dmaone/CommonSense/cortex/PSoC5/io.c

/*
 *
 * Copyright (C) 2016-2017 DMA <dma@ya.ru>
 *
 * This program is free software; you can redistribute it and/or modify
 * it under the terms of the GNU General Public License version 2 as
 * published by the Free Software Foundation.
 */
#include "../io.h"

#include <project.h>
#include <stdio.h>

#include "../gpio.h"
#include "../globals.h"
#include "../scan.h"
#include "../settings.h"

// for xprintf - stdio + stdarg
#include <stdarg.h>

// only allow telemetry every Nth USB tick - see io_has_space.
// This is needed so host isn't too overwhelmed to timely send GET_STATUS
// (if it doesn't - keyboard goes to autonomous mode and telemetry stops!)
#define TELEMETRY_RATELIMIT 10
volatile uint8_t telemetry_cooldown = TELEMETRY_RATELIMIT;  // Block until first io_tick

static bool boot_protocol_mode = false;

typedef struct {
  uint8_t EP;
  uint8_t len;
  uint8_t data[64];
} UsbPdu_t;

#define USB_BUFFER_END 15
#define USB_BUFFER_NEXT(X) ((X + 1) & USB_BUFFER_END)
#define USB_BUFFER_PREV(X) ((X + USB_BUFFER_END) & USB_BUFFER_END)
// ^^^ THIS MUST EQUAL 2^n-1!!! Used as bitmask.

#define KBD_INTERFACE 0
#define KBD_SCB USB_DEVICE0_CONFIGURATION0_INTERFACE0_ALTERNATE0_HID_OUT_RPT_SCB
#define KBD_INBOX USB_DEVICE0_CONFIGURATION0_INTERFACE0_ALTERNATE0_HID_OUT_BUF
#define KBD_OUTBOX USB_DEVICE0_CONFIGURATION0_INTERFACE0_ALTERNATE0_HID_IN_BUF

#define CONSUMER_OUTBOX                                                        \
  USB_DEVICE0_CONFIGURATION0_INTERFACE2_ALTERNATE0_HID_IN_BUF

#define SYSTEM_OUTBOX                                                          \
  USB_DEVICE0_CONFIGURATION0_INTERFACE3_ALTERNATE0_HID_IN_BUF

#define CTRLR_SCB                                                              \
  USB_DEVICE0_CONFIGURATION0_INTERFACE1_ALTERNATE0_HID_OUT_RPT_SCB
#define CTRLR_INBOX USB_DEVICE0_CONFIGURATION0_INTERFACE1_ALTERNATE0_HID_OUT_BUF

UsbPdu_t usbSendingQueue[USB_BUFFER_END + 1];
uint8_t usbSendingReadPos = 0;
uint8_t usbSendingWritePos = 0;

void report_status(void) {
  IN_c2packet_t outbox;
  outbox.response_type = C2RESPONSE_STATUS;
  device_status_t* deviceStatus = (void *)&outbox.payload;
  deviceStatus->status = status_register;
  deviceStatus->versionMajor = DEVICE_VER_MAJOR;
  deviceStatus->versionMinor = DEVICE_VER_MINOR;
  EEPROM_UpdateTemperature();
  deviceStatus->dieTempSign = dieTemperature[0];
  deviceStatus->dieTemp = dieTemperature[1];
  deviceStatus->sysTime = systime;
  io_c2(&outbox);
  // xprintf("time: %d", systime);
  // xprintf("LED status: %d %d %d %d %d", led_status&0x01, led_status&0x02,
  // led_status&0x04, led_status&0x08, led_status&0x10);
}

void process_ewo(OUT_c2packet_t *inbox) {
  bool scan_active = STATUS_IS(C2DEVSTATUS_SCAN_ENABLED);
  status_register = inbox->payload[0];
  // Avoid scan_start if already started - dangerous to do so.
  if (!scan_active && STATUS_IS(C2DEVSTATUS_SCAN_ENABLED)) {
    scan_start();
  }
  report_status();
}

void usb_receive(OUT_c2packet_t *inbox) {
  ticksToAutonomy = SETUP_TIMEOUT;
  switch (inbox->command) {
  case C2CMD_EWO:
    process_ewo(inbox);
    break;
  case C2CMD_GET_STATUS:
    report_status();
    if (STATUS_IS(C2DEVSTATUS_INSANE)) {
      scan_report_insanity();
    }
    break;
  case C2CMD_SET_MODE:
    FORCE_BIT(status_register, C2DEVSTATUS_SETUP_MODE, inbox->payload[0]);
    report_status(); // If FC doesn't get a reply - it will wait 2s for CTS.
    break;
  case C2CMD_ENTER_BOOTLOADER:
    xprintf("Jumping to bootloader..");
    Boot_Load(); // Does not return, no need for break
  case C2CMD_UPLOAD_CONFIG:
    settings_receive_block(inbox);
    break;
  case C2CMD_DOWNLOAD_CONFIG:
    settings_send_block(inbox);
    break;
  case C2CMD_APPLY_CONFIG:
    xprintf("Applying config..");
    SET_BIT(status_register, C2DEVSTATUS_SETUP_MODE);
    settings_apply();
    xprintf("success!");
    break;
  case C2CMD_COMMIT:
    settings_save();
    break;
  case C2CMD_ROLLBACK:
    xprintf("Resetting..");
    CySoftwareReset(); // Does not return, no need for break.
  case C2CMD_ENABLE_TELEMETRY:
    FORCE_BIT(status_register, C2DEVSTATUS_TELEMETRY_MODE, inbox->payload[0]);
    FORCE_BIT(status_register, C2DEVSTATUS_SETUP_MODE, !inbox->payload[0]);
    scan_reset();
    if (!inbox->payload[0]) {
      report_status(); // FC wants reply - if telemetry is off, send status.
    }
    break;
  default:
    break;
  }
}

void usbEnqueue(uint8_t EP, uint8_t len, uint8_t *data) {
  usbSendingWritePos = USB_BUFFER_NEXT(usbSendingWritePos);
  usbSendingQueue[usbSendingWritePos].EP = EP;
  usbSendingQueue[usbSendingWritePos].len = len;
  memcpy(usbSendingQueue[usbSendingWritePos].data, data, len);
}

void usbSend() {
  if (usb_status != USB_STATUS_CONNECTED) {
    return;
  }
  while (usbSendingWritePos != usbSendingReadPos) {
    uint8_t pos = USB_BUFFER_NEXT(usbSendingReadPos);
    UsbPdu_t* item = &usbSendingQueue[pos];
    if (USB_GetEPState(item->EP) == USB_IN_BUFFER_EMPTY) {
      if (boot_protocol_mode && item->EP == KBD_EP) {
        /*
         * In boot protocol mode, send short packets, lest HP Z800 BIOS
         * will get first key stuck until you unplug the keyboard.
         *
         * Which is kinda violation of USB HID Appendix B
         * ("The BIOS will ignore any extensions to reports")
         * but also kinda not ("The report may not exceed 8 bytes in length.")
         * Most BIOSes are fine with 64-byte USB packets, but not HP Z800.
         */
        USB_LoadInEP(item->EP, item->data, 8);
      } else {
        USB_LoadInEP(item->EP, item->data, item->len);
      }
      usbSendingReadPos = pos;
    } else {
      break;
    }
  }
}

bool io_has_space(void) {
  // figuring out if IO is busy based on queue length doesn't work.
  // So we'll just ratelimit to every 10th tick
  if (telemetry_cooldown == 0) {
    telemetry_cooldown = 1;
    return true;
  }
  return false;
}

void io_init(void) {
  usbSendingReadPos = 0;
  usbSendingWritePos = 0;
  pipeline_init();
#ifndef SELF_POWERED
  USB_Start(0u, USB_5V_OPERATION);
#endif
}

void io_tick(void) {
  /* This doesn't work - supposed to, but doesn't.
  if (USB_GetEPState(OUTBOX_EP) == USB_OUT_BUFFER_FULL) {
    OUT_c2packet_t inbox;
    USB_ReadOutEP(OUTBOX_EP, inbox.raw, 64);
    usb_receive(&inbox);
  }
  if (USB_GetEPState(KBD_EP) == USB_OUT_BUFFER_FULL) {
    led_status = KBD_INBOX[0];
    KBD_SCB.status = USB_XFER_IDLE;
    gpio_setLEDs(led_status);
  }
  */
  uint8_t enableInterrupts = CyEnterCriticalSection();
  if (CTRLR_SCB.status == USB_XFER_STATUS_ACK) {
    CTRLR_SCB.status = USB_XFER_IDLE;
    usb_receive((OUT_c2packet_t*)CTRLR_INBOX);
  }
  if (KBD_SCB.status == USB_XFER_STATUS_ACK) {
    led_status = KBD_INBOX[0];
    KBD_SCB.status = USB_XFER_IDLE;
    gpio_setLEDs(led_status);
  }
  CyExitCriticalSection(enableInterrupts);
  if (USB_GetProtocol(KBD_INTERFACE) == 0) {
    io_kro_limit = BOOT_KRO_LIMIT;
    boot_protocol_mode = true;
  } else {
    boot_protocol_mode = false;
    io_kro_limit = KBD_KRO_LIMIT;
    /*
     * honoring SET_IDLE causes M1 MBP to spend 7% of CPU in com.apple.AppleUserHIDDrivers.
     * BLE HID docs say SET_IDLE was meant for autorepeat and is a Bad Idea in modern day.
     * So, this part is disabled.
    if (USB_UpdateHIDTimer(KBD_INTERFACE) == USB_IDLE_TIMER_EXPIRED) {
      // We must report periodically even if no change happened (USB HID 7.2.4)
      // ..except at least Windows just tells us to shut up forever,
      // only reporting when a real change happens.
      io_keyboard();
      io_consumer();
      io_system();
    }
    */
  }
  if (telemetry_cooldown > 0) {
    if (++telemetry_cooldown > TELEMETRY_RATELIMIT) {
      telemetry_cooldown = 0;
    }
  }
  usbSend();
}

void xprintf(const char *format_p, ...) {
#ifndef XPRINTF_ALWAYS_ENABLED
  if (BIT_IS_CLEAR(status_register, C2DEVSTATUS_SETUP_MODE)) {
    return;
  }
#endif
  IN_c2packet_t outbox;
  va_list va;
  va_start(va, format_p);
  vsnprintf((char *)outbox.raw, sizeof(outbox), format_p, va);
  va_end(va);
  io_c2(&outbox);
}

// Auto-timestamped xprintf
void ts_xprintf(const char *format_p, ...) {
#ifndef XPRINTF_ALWAYS_ENABLED
  if (BIT_IS_CLEAR(status_register, C2DEVSTATUS_SETUP_MODE)) {
    return;
  }
#endif
  IN_c2packet_t outbox;
  va_list va;
  va_start(va, format_p);
  log_message_t* msg = (log_message_t*)&outbox.raw;
  vsnprintf(msg->message, sizeof(msg->message), format_p, va);
  va_end(va);
  msg->response_type = C2RESPONSE_LOG_MESSAGE;
  msg->sysTime = systime;
  io_c2(&outbox);
}


void coded_timestamped_message(coded_message_t* msg) {
#ifndef CODED_MESSAGES_ALWAYS_ENABLED
  if (BIT_IS_CLEAR(status_register, C2DEVSTATUS_SETUP_MODE)) {
    return;
  }
#endif
  msg->response_type = C2RESPONSE_CODED_MESSAGE;
  msg->sysTime = systime;
  io_c2((IN_c2packet_t*)msg);
}

#if NOT_A_KEYBOARD == 1
#define _WIPE_OUTBOX(OUTBOX) memset(OUTBOX, 0, OUTBOX_SIZE(OUTBOX))
#else
#define _WIPE_OUTBOX(OUTBOX)
#endif

#define USB_SEND_REPORT(TYPE, BUFFER)                                          \
  _WIPE_OUTBOX(TYPE##_OUTBOX);                                                 \
  usbEnqueue(TYPE##_EP, OUTBOX_SIZE(TYPE##_OUTBOX), (void*)BUFFER);

inline void io_keyboard() {
  USB_SEND_REPORT(KBD, keyboard_report);
}

inline void io_consumer() {
  USB_SEND_REPORT(CONSUMER, consumer_report);
}

inline void io_system() {
  USB_SEND_REPORT(SYSTEM, system_report);
}

void io_c2(IN_c2packet_t* data) {
  usbEnqueue(OUTBOX_EP, sizeof(data->raw), data->raw);
}
