dmaone/CommonSense/c2/c2_protocol.h

/*
 *
 * Copyright (C) 2016 DMA <dma@ya.ru>
 *
 * This program is free software; you can redistribute it and/or modify
 * it under the terms of the GNU General Public License version 2 as
 * published by the Free Software Foundation.
 */

#pragma once

#include <stdint.h>

/*
 *** CAUTION *** VORSICHT *** ATTENTION *** berhati-hati
 * This include is for firmware side. C99 only.
 * All constants MUST be #defines, no constexprs.
 * String dictionaries, hostname limits like number of switch types
 * are all belong to c2_protocol_hostside.h
 *** CAUTION *** VORSICHT *** ATTENTION *** berhati-hati
 */

#define ABSOLUTE_MAX_ROWS 16
#define ABSOLUTE_MAX_COLS 24
#define ABSOLUTE_MAX_LAYERS 8
#define ABSOLUTE_MAX_PEDALS 8
#define NUM_DELAYS 16
// Careful when changing above - may need to check nvram.h sizes.

#define BOOTLOADER_MAX_PACKET_LENGTH 32
#define BOOTLOADER_PAYLOAD_LENGTH (3 + BOOTLOADER_MAX_PACKET_LENGTH + 3)

#if (CY_PSOC5LP)
// firmware AND PSoC5LP - limit to 64 bytes
#define C2_MTU 64
#else
#define C2_MTU 130
#endif
/*
 * Windows 10 HID requires 4 bytes of MTU (both ATT and L2CAP) and DLE headroom
 * to work. So min. BLE MTU value needs to be 134.
 * TODO: fix explanation below (for USB it's still true!)
 *
 * The data block for the control channel is 64 bytes, both up and down.
 * Packet format is [command byte][application-specific].
 * MESSAGES MUST BE EXACTLY 64 BYTES IN LENGTH, otherwise host will drop them.
 * If your message is longer - it is _your_ problem, you should handle it at
 * both sides. Use the IN_type_t and OUT_type_t for communication. Directions
 * are defined in USB spec sense - so IN is TO HOST, OUT is TO DEVICE. Preferred
 * method of handling messages at the host is to install event handler to TODO
 * On firmware side we should conserver resources,
 * so use case statement in dispatch_command. Do not use
 * USB_EP_INBOX_EP_ISR_ExitCallback! Messages that are NOT picked up will be
 * DROPPED at firmware side or PRINTED at the host side. They will be printed in
 * full, first byte included. This kind of restricts number of available
 * commands to 32. Should be enough for everyone!
 *
 */

enum c2command {
  C2CMD_EWO = 0x00,
  C2CMD_GET_STATUS = 0x01,
  C2CMD_ENTER_BOOTLOADER = 0x02,
  // DO NOT TOUCH THOSE THREE ABOVE!
  // Bootloader command must keep it's place or you lose firmware update
  // capability.
  C2CMD_UPLOAD_CONFIG,   // FROM host
  C2CMD_DOWNLOAD_CONFIG, // TO host
  C2CMD_APPLY_CONFIG,    // reinits sensitive parts
  C2CMD_COMMIT,
  C2CMD_ROLLBACK,
  C2CMD_SET_MODE,
  C2CMD_ENABLE_TELEMETRY
};

enum c2response {
  C2RESPONSE_STATUS = 0x00,
  C2RESPONSE_CONFIG,
  C2RESPONSE_CODED_MESSAGE,
  C2RESPONSE_TELEMETRY_ROW,
  C2RESPONSE_LOG_MESSAGE,
};

enum deviceStatus {
  C2DEVSTATUS_SCAN_ENABLED = 0,
  C2DEVSTATUS_OUTPUT_ENABLED,
  C2DEVSTATUS_TELEMETRY_MODE,
  C2DEVSTATUS_SETUP_MODE,
  C2DEVSTATUS_INSANE,
  C2DEVSTATUS_WRONG_NVRAM,
};

enum deviceMode {
  C2DEVMODE_NORMAL = 0,
  C2DEVMODE_SETUP,
};

enum expMode {
  EXP_MODE_DISABLED = 0,

  EXP_MODE_SOLENOID_NUMCAPS,
  EXP_MODE_LEDS,
};

enum SwitchType {
  ST_BEAMSPRING = 0,
  ST_BUCKLING_SPRING,
  ST_ADB,
  ST_SUN,
  ST_MAGVALVE,
  ST_MICROSWITCH,
  ST_CONTACT,
  ST_UNKNOWN,
};

enum HostMode {
  HM_WINDOWS = 0,
  HM_MAC = 1,
};



enum MessageCode {
  MC_KEYPRESS = 0,
  MC_KEY_RESOLVED,
  MC_SCHEDULE_HID,
  MC_PROCESS_HID,
};

typedef union {
  struct {
    uint8_t status;
    uint8_t versionMajor;
    uint8_t versionMinor;
    uint8_t dieTempSign;
    uint8_t dieTemp;
    uint8_t padding0;
    uint8_t padding1;
    uint8_t padding2;
    uint32_t sysTime;
  } __attribute__((packed));
  uint8_t raw[12];
} device_status_t;

typedef union {
  struct {
    uint8_t response_type;
    uint8_t payload[(C2_MTU - 1)];
  } __attribute__((packed));
  uint8_t raw[(C2_MTU)];
} IN_c2packet_t;

// IN_c2packet_t alternative layouts BEGIN
typedef struct {
  uint8_t response_type;
  uint8_t messageCode;
  union {
    uint8_t rawMessage[(C2_MTU - 2)];
    struct {
      uint8_t message[(C2_MTU - 6)];
      uint32_t sysTime;
    } __attribute__((packed));
  };
} __attribute__((packed)) coded_message_t;

// CodedMessage payload layouts - starts at [2], pls keep wider things aligned.
typedef struct {
  uint8_t key;
  uint8_t flags;
} __attribute__((packed)) mc_keypress_t;

typedef struct {
  uint8_t key;
  uint8_t flags;
  uint8_t layer;
  uint8_t code;
} __attribute__((packed)) mc_key_resolved_payload_t;

typedef struct {
  uint8_t code;
  uint8_t flags;
  uint32_t event_time;
  uint8_t position;
  uint8_t data_begin;
  uint8_t data_end;
} __attribute__((packed)) mc_schedule_hid_payload_t;

typedef struct {
  uint8_t code;
  uint8_t flags;
  uint32_t event_time;
  uint8_t position;
  uint8_t data_begin;
  uint8_t data_end;
} __attribute__((packed)) mc_process_hid_payload_t;
// CodedMessage payload layouts END

typedef struct {
  uint8_t response_type;
  union {
    struct {
      char message[(C2_MTU - 5)];
      uint32_t sysTime;
    } __attribute__((packed));
    char raw_message[(C2_MTU - 1)];
  };
} __attribute__((packed)) log_message_t;

// IN_c2packet_t layouts END

typedef union {
  struct {
    unsigned char command;
    unsigned char payload[(C2_MTU - 1)];
  } __attribute__((packed));
  uint8_t raw[(C2_MTU)];
} OUT_c2packet_t;

typedef union {
  struct {
    uint8_t sop;
    uint8_t command;
    uint16_t length; // Thank Cypress for being little-endian!
    // ^^^^4 bytes
    unsigned char payload[BOOTLOADER_PAYLOAD_LENGTH]; // 1B array, 2B row, 32
                                                      // bytes data, +2B
                                                      // checksum +1b stop
                                                      // marker
  } __attribute__((packed));
  uint8_t raw[4 + BOOTLOADER_PAYLOAD_LENGTH];
} Bootloader_packet_t;

typedef union {
  struct {
    uint16_t checksum; // Thank Cypress for being little-endian!
    uint8_t eop;
  } __attribute__((packed));
  uint8_t raw[3];
} Bootloader_packet_trailer_t;

#define CONFIG_TRANSFER_SIZE_BLE 128
#define CONFIG_TRANSFER_SIZE_USB 32
#define CONFIG_BLOCK_DATA_OFFSET 1

#define MACRO_TYPE_ONKEYDOWN 0x00
#define MACRO_TYPE_ONKEYUP 0x80
#define MACRO_TYPE_TAP 0x40
#define MACRO_TYPE_MASK (MACRO_TYPE_ONKEYUP | MACRO_TYPE_TAP)

/* Macro serialization format: [Header, list<Command> AS data]
 * Header: [8b usb code, 8b options, 8b data length]
 * Command: [2b cmd, 4b delayIndex, 2b options, ?8b[usb code]]
 */
enum MacroCmdType {
  MACROCMD_TYPE = 0, // Press-wait-release (code)
  MACROCMD_ACTUATE = 1, // [1b up/down, 1b unused] (code),
  MACROCMD_IGNORED = 2, // initially planned mods state stack ops, presently DNU
  MACROCMD_WAIT = 3,
};
#define MACROCMD_CMD_SHIFT 6
#define MACROCMD_DELAY_SHIFT 2
#define MACROCMD_DELAY_MASK 0b00111100
#define MACROCMD_ACTUATE_KEYUP 0x02

#define MIN_MAC_HID_DELAY 40  // This is here due to ARM MacOS HID horrible slowness.
#define MIN_MAC_CONTROL_DELAY 40  // min delay between unsolicited control packets.

#define DELAYS_EVENT 0  // How fast we can type into USB
#define DELAYS_TAP 1

#define SKIP_SCAN 0

// IMPORTANT - MUST NOT BE A REAL KEY! Easy for beamspring, less so for F122
// with it's 8x16 matrix.
#define COMMONSENSE_NOKEY 255

#define HID_RELEASED_MASK 0x80
#define HID_REAL_KEY_MASK 0x40

#define PEDAL_EDGE_TRIGGERED 0x01
#define PEDAL_NORMALLY_HIGH 0x02
#define PEDAL_LED_SYNCED 0x04

// serial stuff
enum supervisory_command {
  SUP_CMD_NOOP = 0,
  SUP_CMD_KEYDOWN = 'p',
  SUP_CMD_KEYUP = 'r',
  SUP_CMD_SUSPEND = 's',
  SUP_CMD_WAKEUP = 'w',
  SUP_CMD_CLEAR = 'c',
};

typedef union {
  struct {
    char command;
    uint8_t data;
  } __attribute__((packed));
  uint8_t raw[2];
} Sup_Pdu_t;
