dmaone/CommonSense/cortex/PSoC5/settings.c

/*
 *
 * Copyright (C) 2023 DMA <dma@ya.ru>
 *
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
 */
#include "../settings.h"
#include "../io.h"
#include "../scan.h"
#include "../gpio.h"
#include "../io.h"

void settings_receive_block(OUT_c2packet_t *inbox) {
  if (status_register != (1 << C2DEVSTATUS_SETUP_MODE)) {
    xprintf("Invalid status register for config upload");
    return;
  }
  uint32_t offset = inbox->payload[0] * CONFIG_TRANSFER_SIZE_USB;
  if (offset < EEPROM_BYTESIZE) {
    memcpy(config.raw + offset, inbox->payload + CONFIG_BLOCK_DATA_OFFSET,
      CONFIG_TRANSFER_SIZE_USB);
  } else {
    xprintf("Packet %d beyond NVRAM boundaries!", inbox->payload[0]);
  }
  IN_c2packet_t outbox;
  outbox.response_type = C2RESPONSE_CONFIG;
  outbox.payload[0] = inbox->payload[0];
  io_c2(&outbox);
}

void settings_send_block(OUT_c2packet_t *inbox) {
  IN_c2packet_t outbox;
  outbox.response_type = C2RESPONSE_CONFIG;
  outbox.payload[0] = inbox->payload[0];
  uint32_t offset = inbox->payload[0] * CONFIG_TRANSFER_SIZE_USB;
  if (offset < EEPROM_BYTESIZE) {
    memcpy(outbox.payload + CONFIG_BLOCK_DATA_OFFSET, config.raw + offset,
      CONFIG_TRANSFER_SIZE_USB);
  } else {
    xprintf("Packet %d beyond NVRAM boundaries!", inbox->payload[0]);
  }
  io_c2(&outbox);
}

void settings_sanitize(void) {
  if (config.matrixRows != MATRIX_ROWS || config.matrixCols != MATRIX_COLS) {
    // Yeehaw, a virgin EEPROM (or a different matrix size reflash)
    memset(config.thresholds, 0, sizeof(config.thresholds));
    config.configVersion = CS_CONFIG_VERSION;
  }
  config.matrixRows = MATRIX_ROWS;
  config.matrixCols = MATRIX_COLS;
  config.matrixLayers = MATRIX_LAYERS;
  config.switchType = SWITCH_TYPE;
  config.pedals = NUM_PEDALS;
  switch (config.adcBits) {
    case 8:
    case 10:
    case 12:
      break;
    default:
      // People don't read docs hence can't find this setting. 12 bit usually 
      // not enough to go overboard, so let's default to 12 bits and deal with
      // possible "help I'm gone 3-digit" if those ever happen.
      config.adcBits = 12; 
  };
  if (config.chargeDelay < MIN_CHARGE_DELAY) {
    config.chargeDelay = MIN_CHARGE_DELAY;
  };
  if (config.dischargeDelay < MIN_DISCHARGE_DELAY) {
    config.dischargeDelay = MIN_DISCHARGE_DELAY;
  }
  if (config.debouncingTicks < 1) {
    config.debouncingTicks = DEFAULT_DEBOUNCING_TICKS;
  }
  if (config.hostMode == HM_MAC
  && config.delayLib[DELAYS_EVENT] < MIN_MAC_HID_DELAY) {
    config.delayLib[DELAYS_EVENT] = MIN_MAC_HID_DELAY;
  }
}

void settings_load(void) {
  EEPROM_Start();
  CyDelayUs(5);
  // Copypaste from EEPROM.c/EEPROM_ReadByte! Use with caution!
  uint8 interruptState;
  interruptState = CyEnterCriticalSection();
  /* Request access to EEPROM for reading.
  This is needed to reserve PHUB for read operation from EEPROM */
  CyEEPROM_ReadReserve();
  memcpy(config.raw, (void *)CYDEV_EE_BASE, CYDEV_EE_SIZE);
  /* Release EEPROM array */
  CyEEPROM_ReadRelease();
  CyExitCriticalSection(interruptState);
  EEPROM_Stop();
  settings_sanitize();
  if (config.configVersion < CS_LAST_COMPATIBLE_NVRAM_VERSION) {
    status_register = (1 << C2DEVSTATUS_WRONG_NVRAM) |
                      (1 << C2DEVSTATUS_INSANE) |
                      (1 << C2DEVSTATUS_SETUP_MODE);
    xprintf("Incompatible NVRAM layout!");
    return;
  }
  if (config.configVersion != CS_CONFIG_VERSION) {
    xprintf("Old version of EEPROM - possibly unpredictable results.");
  }
}

void settings_apply(void) {
  gpio_init();
  pipeline_init(); // calls scan_reset
  scan_init(config.debouncingTicks);
  scan_start();
}

void settings_save(void) {
  settings_sanitize();
  EEPROM_Start();
  CyDelayUs(5);
  EEPROM_UpdateTemperature(); // Unlikely to rise 10C during operation.
  xprintf("Updating EEPROM GO!");
  uint16_t bytes_modified = 0;
  uint8_t blocks_written = 0;
  for (uint8_t row = 0; row < (EEPROM_BYTESIZE >> 4); row++) {
    uint16_t row_start = row << 4;
    uint8_t* rowData = config.raw + row_start;
    bool needs_write = false;
    for (uint8_t i = 0; i < 16; i++) {
      if (rowData[i] != EEPROM_ReadByte(row_start + i)) {
        needs_write |= true;
        bytes_modified++;
      }
    }
    if (needs_write) {
      EEPROM_Write(rowData, row);
      blocks_written++;
    }
  }
  EEPROM_Stop();
  xprintf("Written %d bytes/%d blocks!", bytes_modified, blocks_written);
}
