dmaone/CommonSense/FlightController/settings.h

#pragma once

#include <QSettings>

#define SETTINGS_DIR_KEY "settings_dir"
#define DEVICECONFIG_DIR_KEY SETTINGS_DIR_KEY
#define LAYOUTS_DIR_KEY SETTINGS_DIR_KEY

#define FIRMWARE_FILE_KEY "firmware_file"
